mkhairyx/DIY_Mini_Marauder/source/Blender - Renders/Render.png

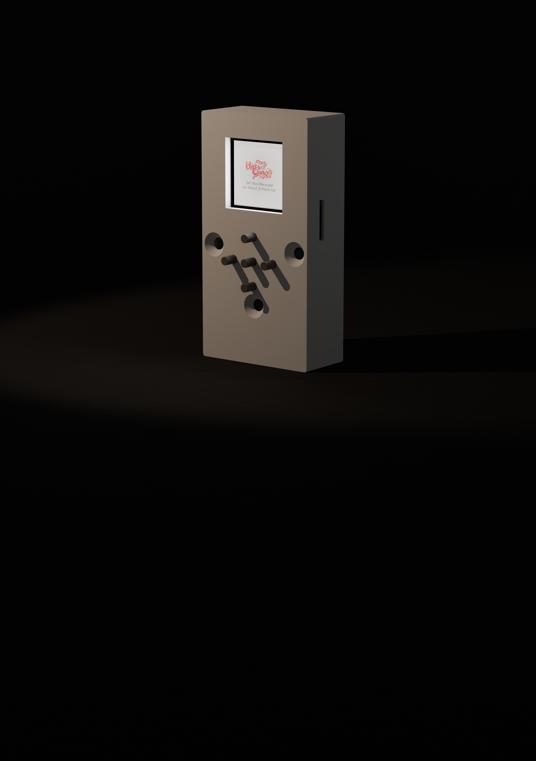
source/Blender - Renders/Render.png
