mkhairyx/DIY_Mini_Marauder/source/KiCad - PCB/DIY_Mini_Marauder/reverse resources/tf.png

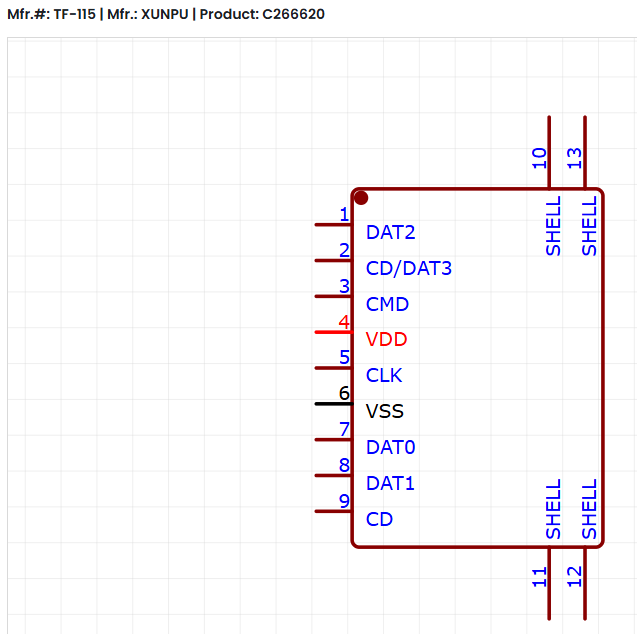
source/KiCad - PCB/DIY_Mini_Marauder/reverse resources/tf.png
