mkhairyx/DIY_Mini_Marauder/source/KiCad - PCB/DIY_Mini_Marauder/sourcing components/Screenshot 2026-06-08 201428.png

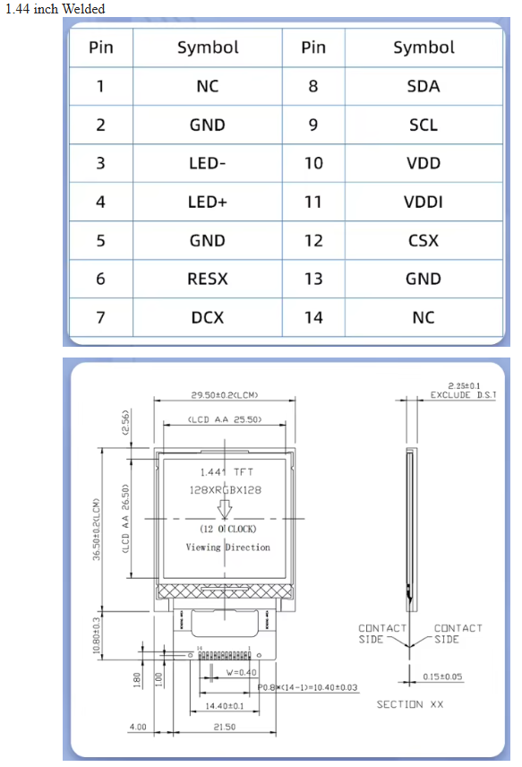
source/KiCad - PCB/DIY_Mini_Marauder/sourcing components/Screenshot 2026-06-08 201428.png
